RexiclesPrime/MotorcycleSlotMachine/assets/pixel/1bit/jp_x4.png

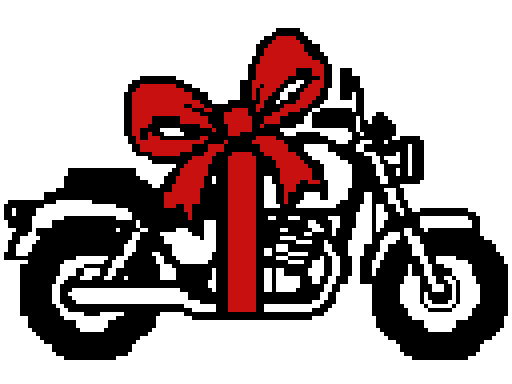
assets/pixel/1bit/jp_x4.png
