RexiclesPrime/MotorcycleSlotMachine/assets/pixel/1bit/r7_x4.png

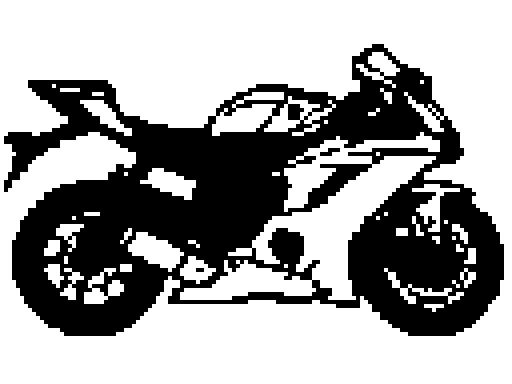
assets/pixel/1bit/r7_x4.png
