RexiclesPrime/MotorcycleSlotMachine/assets/pixel/src/jp.jpg

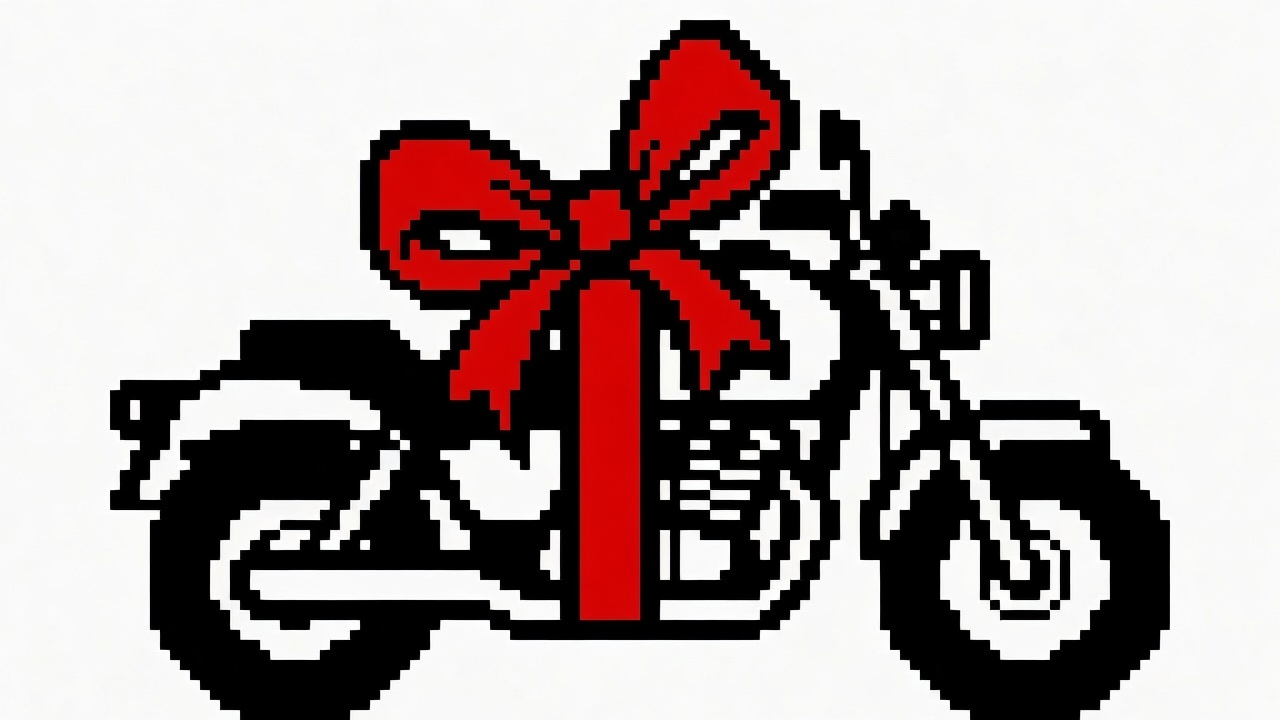
assets/pixel/src/jp.jpg
