RexiclesPrime/MotorcycleSlotMachine/assets/pixel/src/r7.jpg

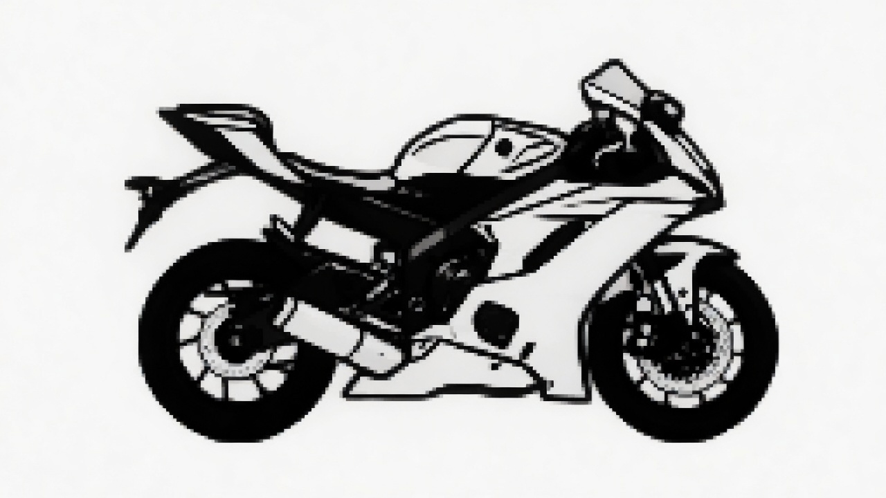
assets/pixel/src/r7.jpg
