RexiclesPrime/MotorcycleSlotMachine/assets/pixel/src/tt.jpg

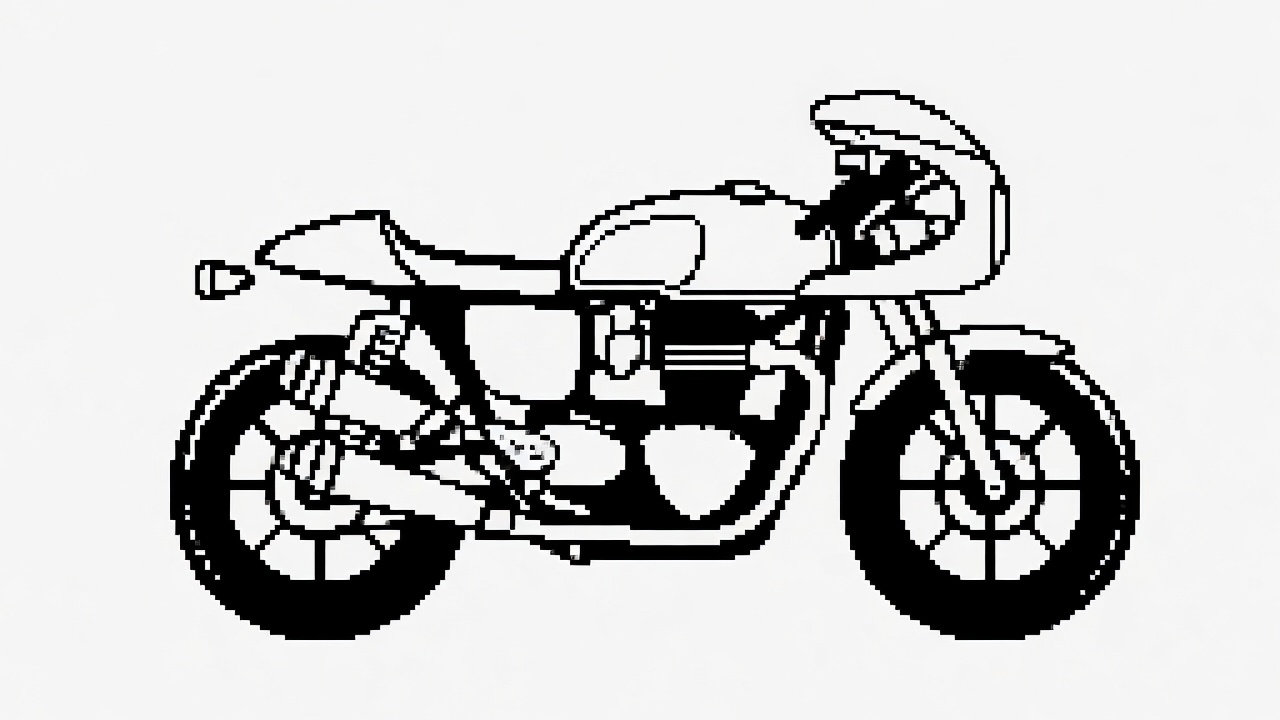
assets/pixel/src/tt.jpg
